Zefrors/Micromouse-2026/mm26_REAL/Core/Inc/motors.h

#include "main.h"

typedef enum motor {left, right} motor;
typedef enum direction {forward, back} direction;

void setMotorSpeed(motor side, uint16_t speed, direction dir);
int16_t getMotorEnc(motor side);
void setMotorEnc(motor side, int16_t encVal);
