Zefrors/Micromouse-2026/mm26_REAL/Core/Inc/ftoa.h

/**
 *  stm32tpl --  STM32 C++ Template Peripheral Library
 *  Visit https://github.com/antongus/stm32tpl for new versions
 *
 *  Copyright (c) 2011-2020 Anton B. Gusev aka AHTOXA
 *
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
 *
 *  file         : ftoa.h
 *  description  : convert double to string
 *
 */

#ifndef STM32TPL_FTOA_H_INCLUDED
#define STM32TPL_FTOA_H_INCLUDED

#ifdef __cplusplus
extern "C" {
#endif

char * ftoa(double f, char * buf, int precision);

#ifdef __cplusplus
}
#endif

#endif // STM32TPL_FTOA_H_INCLUDED
